valeriosetti/ploopy-nano-kicad/result/closed-trackball.jpg

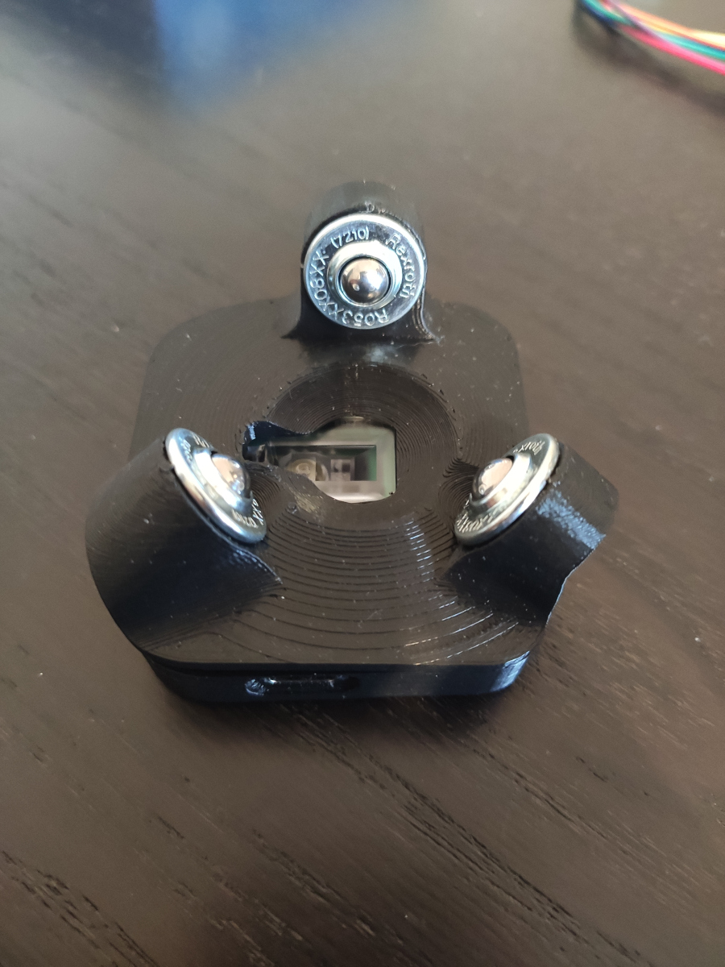
result/closed-trackball.jpg
